Prokuon/MeshT1/Model/buzzer.SLDPRT

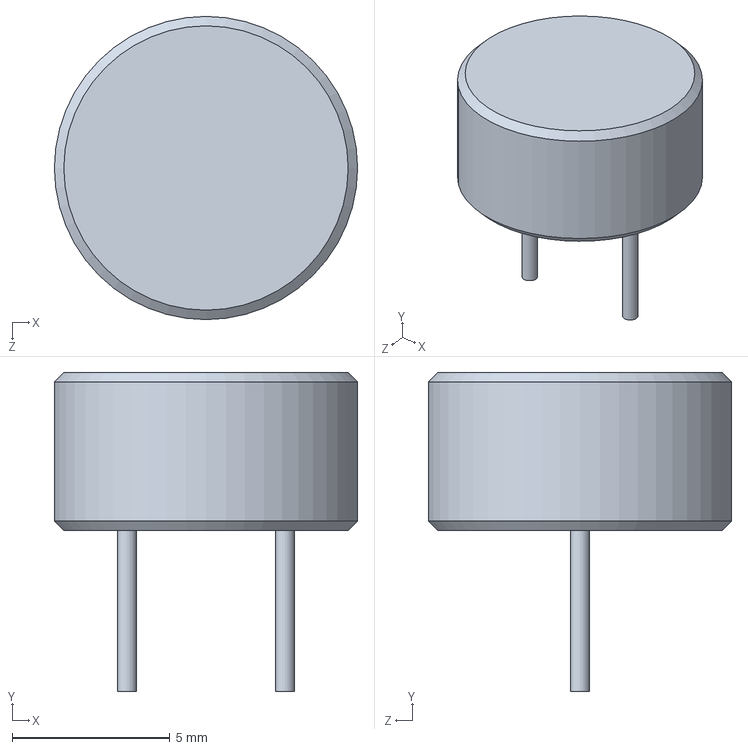
[picture p23: CAD file, 2025-09-28]
Model/buzzer.SLDPRT
9.60 x 10.1 x 9.60 mm
