Prokuon/MeshT1/Model/tm-2024a.SLDPRT

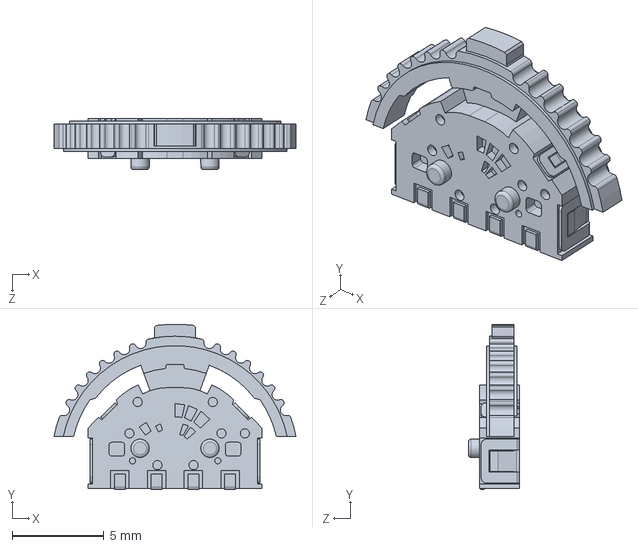
[picture p24: CAD file, 2025-09-28]
Model/tm-2024a.SLDPRT
13.2 x 8.99 x 2.80 mm
