Prokuon/MeshT1/Model/case_L1.SLDPRT

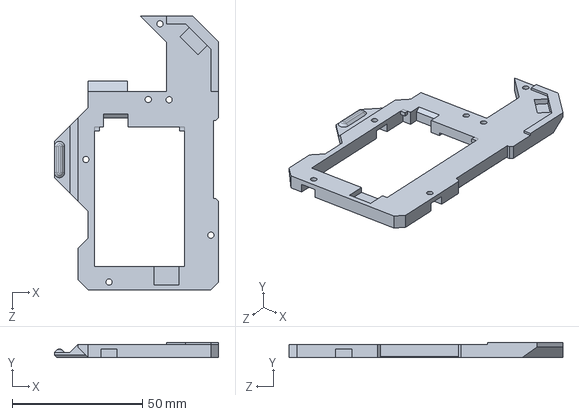
[picture p25: CAD file, 2025-09-28]
Model/case_L1.SLDPRT
63.0 x 5.80 x 105.0 mm
