Prokuon/MeshT1/Model/case_C4.SLDPRT

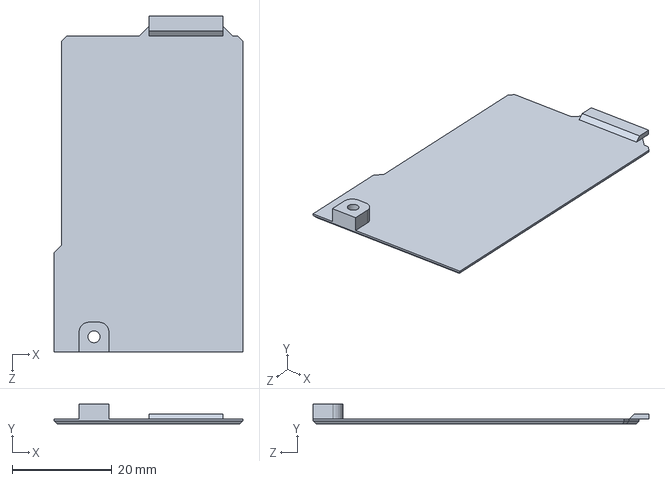
[picture p26: CAD file, 2025-09-28]
Model/case_C4.SLDPRT
37.9 x 4.00 x 67.5 mm
