Prokuon/MeshT1/Model/case_S2.SLDPRT

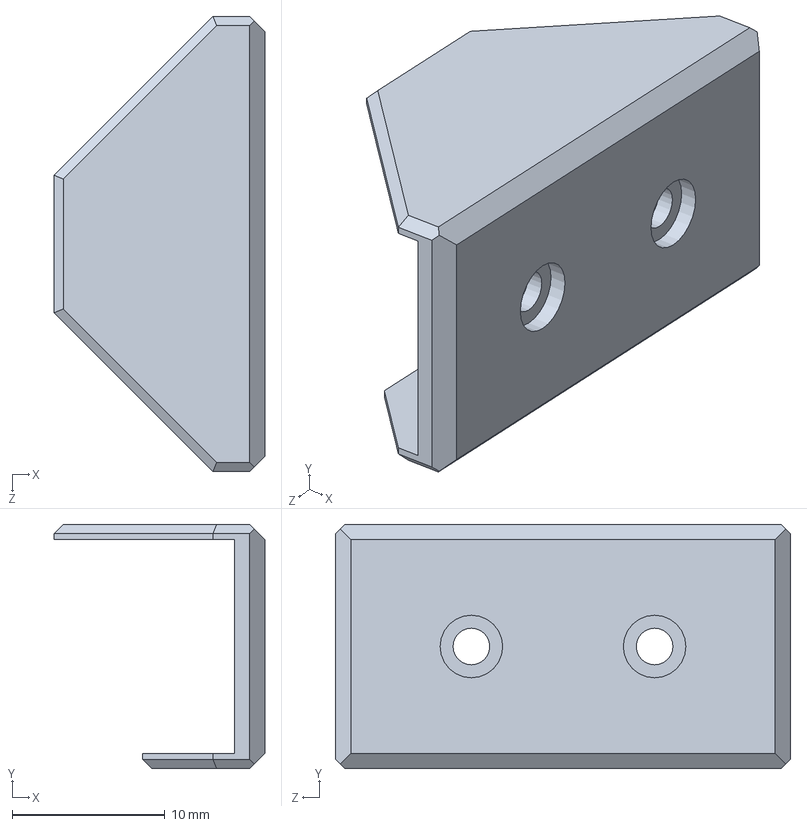
[picture p27: CAD file, 2025-09-28]
Model/case_S2.SLDPRT
13.8 x 16.0 x 29.8 mm
